FeatureNAB/air-sensor/PCB/3d_models/CONN-SMD_SM03B-SRSS-TB-LF-SN-P.step

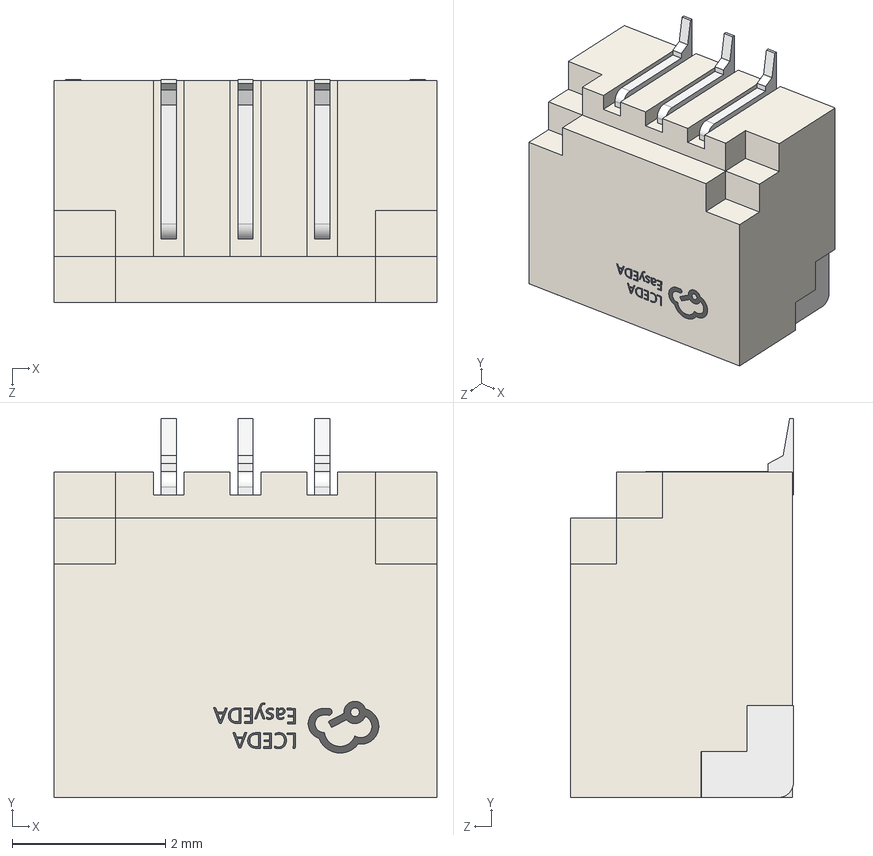
[picture p18: CAD file, 2026-06-08]
PCB/3d_models/CONN-SMD_SM03B-SRSS-TB-LF-SN-P.step
5.00 x 4.95 x 2.91 mm
