FeatureNAB/air-sensor/PCB/3d_models/SOT-23.step

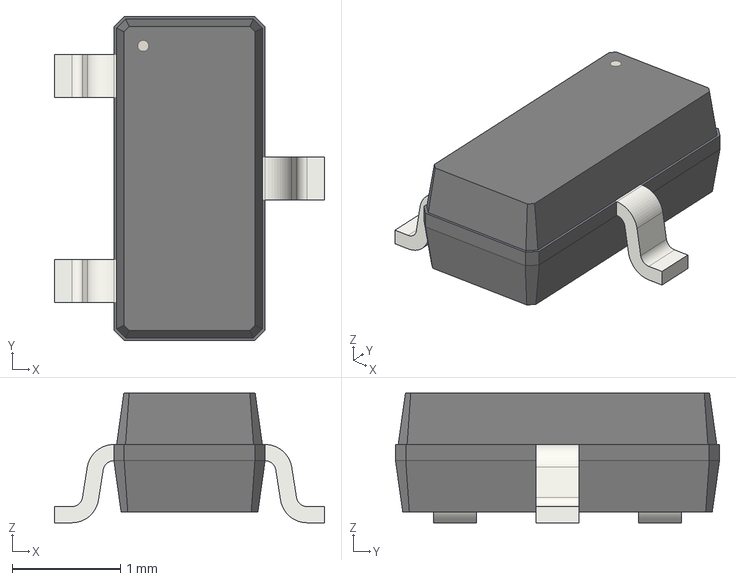
[picture p19: CAD file, 2026-06-08]
PCB/3d_models/SOT-23.step
2.50 x 3.00 x 1.20 mm
