FeatureNAB/air-sensor/PCB/3d_models/CONN-TH_2P-P5.08_WJ2EDGRC-5.08-2P.step

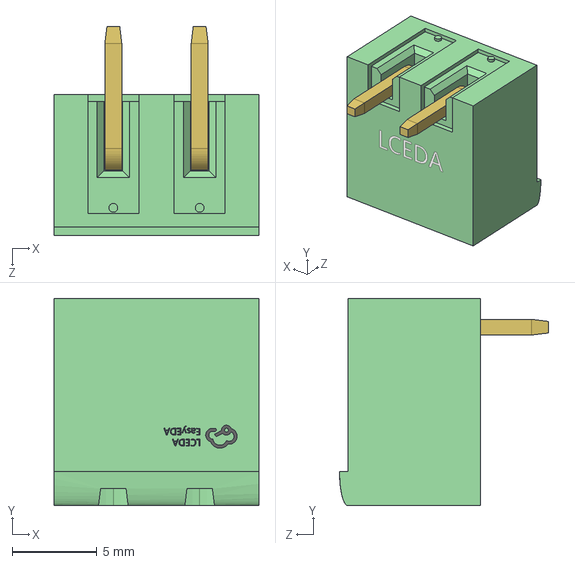
[picture p20: CAD file, 2026-06-08]
PCB/3d_models/CONN-TH_2P-P5.08_WJ2EDGRC-5.08-2P.step
12.1 x 12.2 x 12.3 mm
