FeatureNAB/air-sensor/PCB/3d_models/SOT-23-5.step

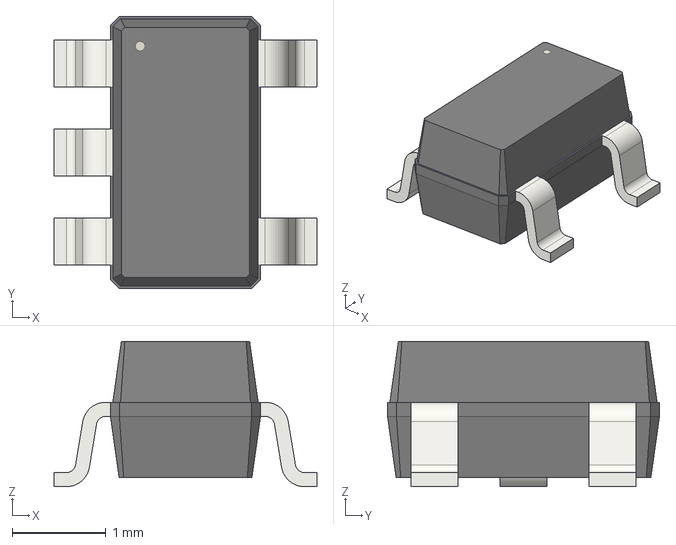
[picture p21: CAD file, 2026-06-08]
PCB/3d_models/SOT-23-5.step
2.80 x 2.90 x 1.55 mm
