FeatureNAB/air-sensor/PCB/3d_models/SOIC-8_L5.0-W4.0-P1.27-LS6.0-BL.step

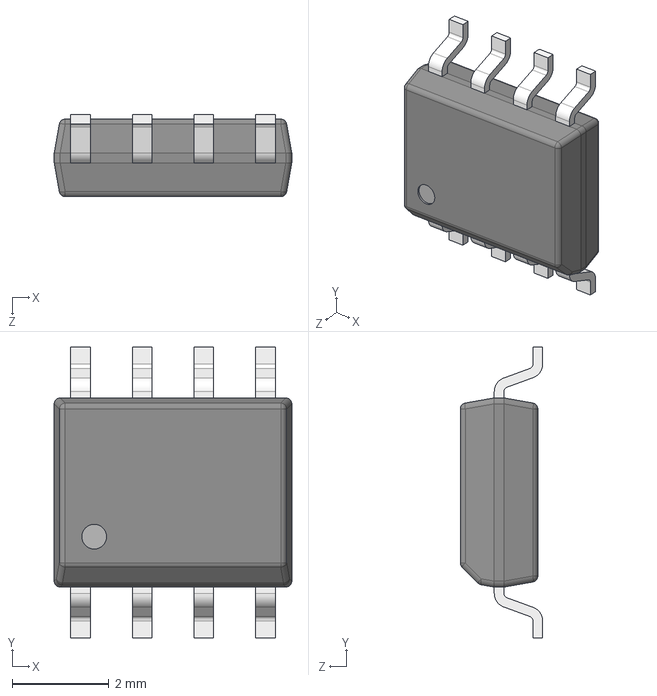
[picture p22: CAD file, 2026-06-08]
PCB/3d_models/SOIC-8_L5.0-W4.0-P1.27-LS6.0-BL.step
4.90 x 6.00 x 1.70 mm
