FeatureNAB/air-sensor/PCB/3d_models/SHTC3.step

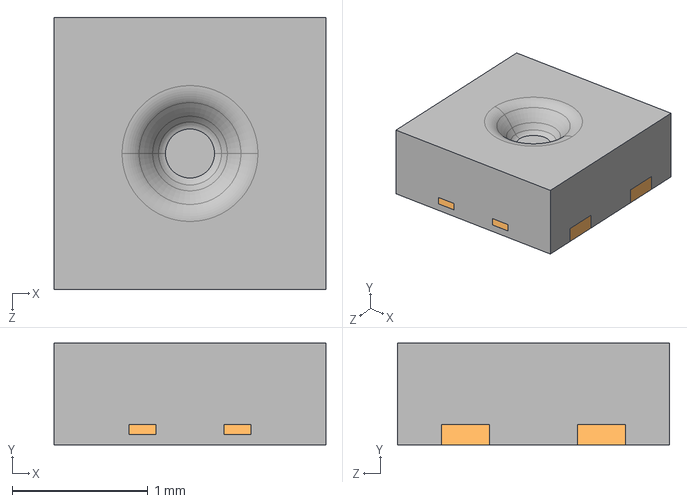
[picture p23: CAD file, 2026-06-08]
PCB/3d_models/SHTC3.step
2.00 x 0.75 x 2.00 mm
