FeatureNAB/air-sensor/PCB/3d_models/WSON-6_1.5x1.5mm_P0.5mm.step

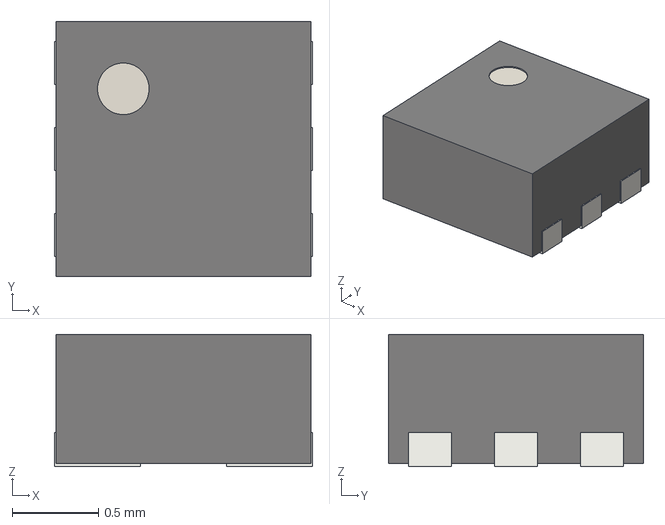
[picture p24: CAD file, 2026-06-08]
PCB/3d_models/WSON-6_1.5x1.5mm_P0.5mm.step
1.50 x 1.48 x 0.77 mm
