FeatureNAB/air-sensor/PCB/3d_models/IND-SMD_L5.2-W5.2_MCW-0530.step

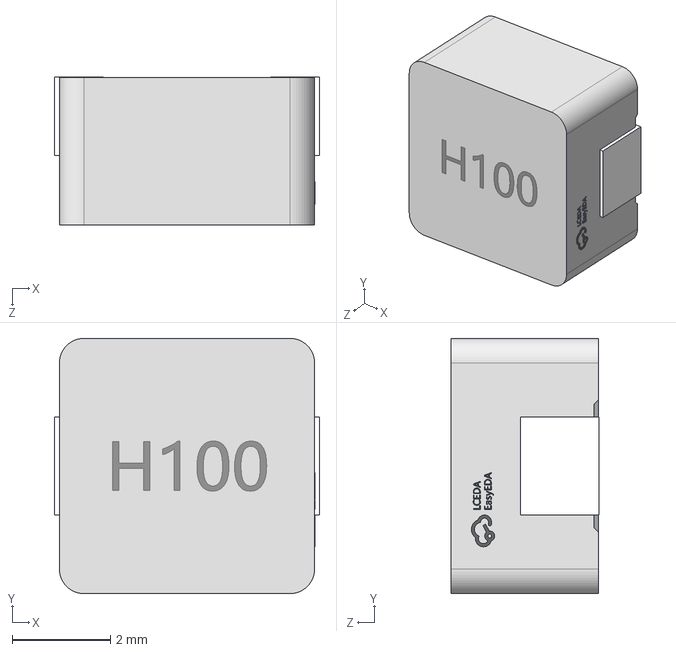
[picture p25: CAD file, 2026-06-08]
PCB/3d_models/IND-SMD_L5.2-W5.2_MCW-0530.step
5.40 x 5.20 x 3.01 mm
